Zquang-88/robocon-2026/hardwave/MP1584/d-sun-dc-dc-step-down-voltage-regulator-simple-version-1.snapshot.4/render/D-SUN_dcdc_step_down_SIMPLE1.png

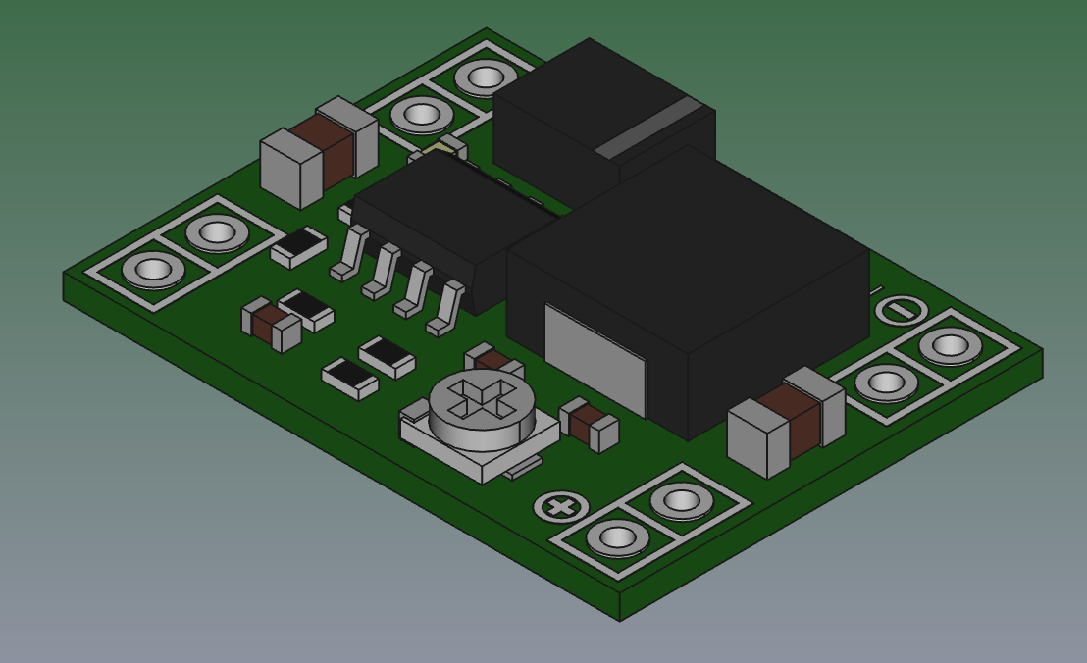
hardwave/MP1584/d-sun-dc-dc-step-down-voltage-regulator-simple-version-1.snapshot.4/render/D-SUN_dcdc_step_down_SIMPLE1.png
