Zquang-88/robocon-2026/.codex-analysis/latest-video-contact.jpg

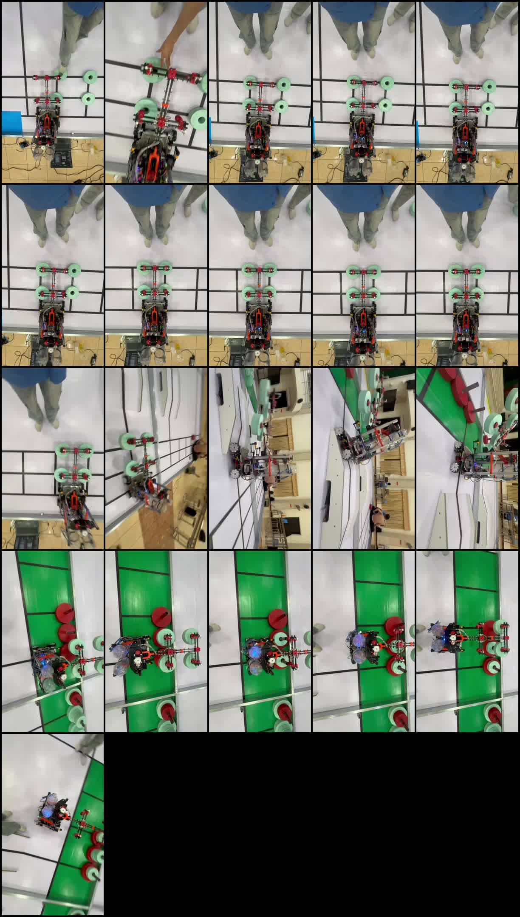
.codex-analysis/latest-video-contact.jpg
