Zquang-88/robocon-2026/analysis/bridge_flip_video/contact_2fps.jpg

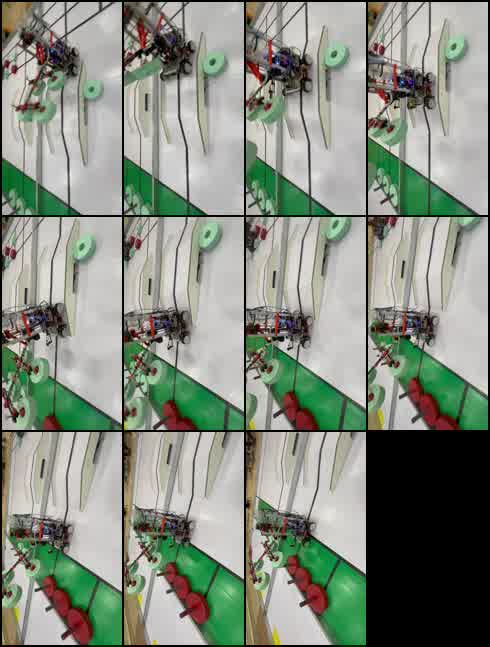
analysis/bridge_flip_video/contact_2fps.jpg
