Zquang-88/robocon-2026/analysis/bridge_flip_video/contact_5fps.jpg

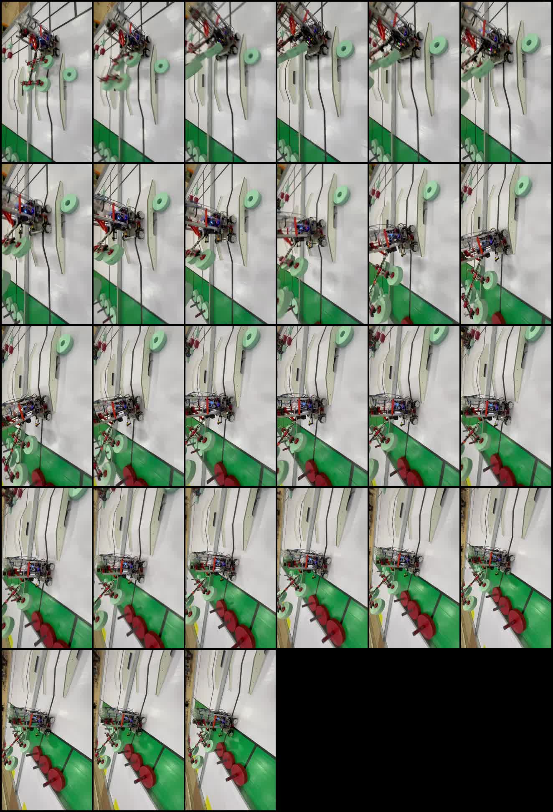
analysis/bridge_flip_video/contact_5fps.jpg
