Zquang-88/robocon-2026/analysis/bridge_flip_video/detail_2p8_5p3.jpg

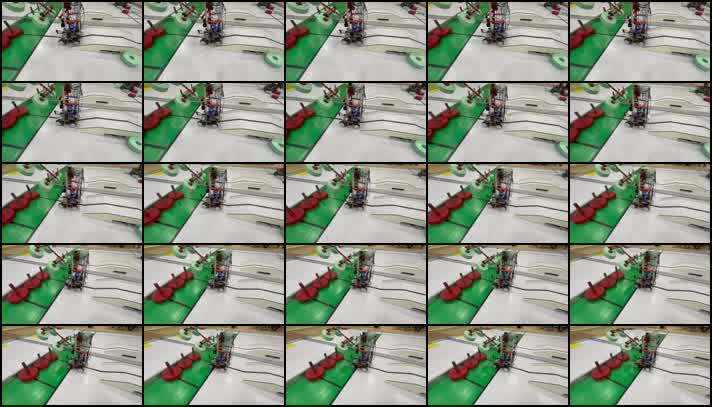
analysis/bridge_flip_video/detail_2p8_5p3.jpg
