Zquang-88/robocon-2026/analysis/bridge_flip_video/keyframes.jpg

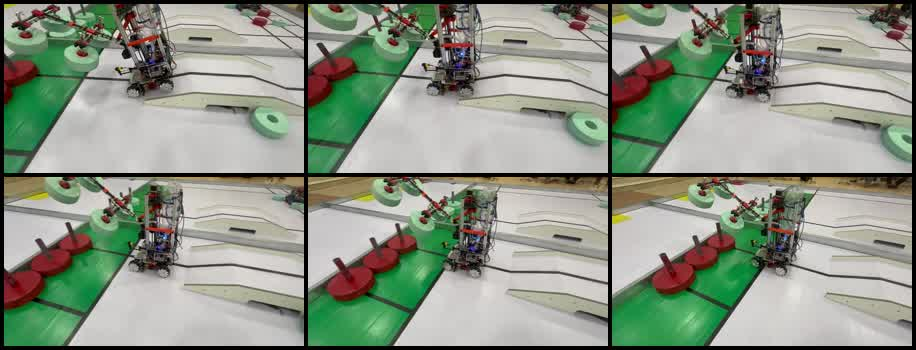
analysis/bridge_flip_video/keyframes.jpg
