Zquang-88/robocon-2026/analysis/bridge_flip_video/tip_sequence.jpg

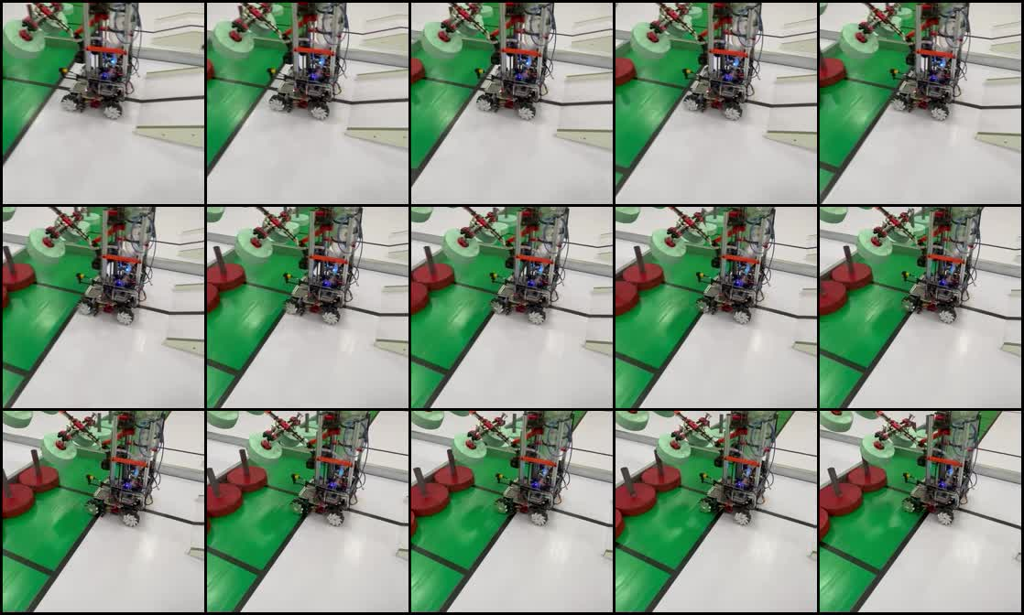
analysis/bridge_flip_video/tip_sequence.jpg
