Zquang-88/robocon-2026/analysis/bridge_run_sync/bridge_1fps.jpg

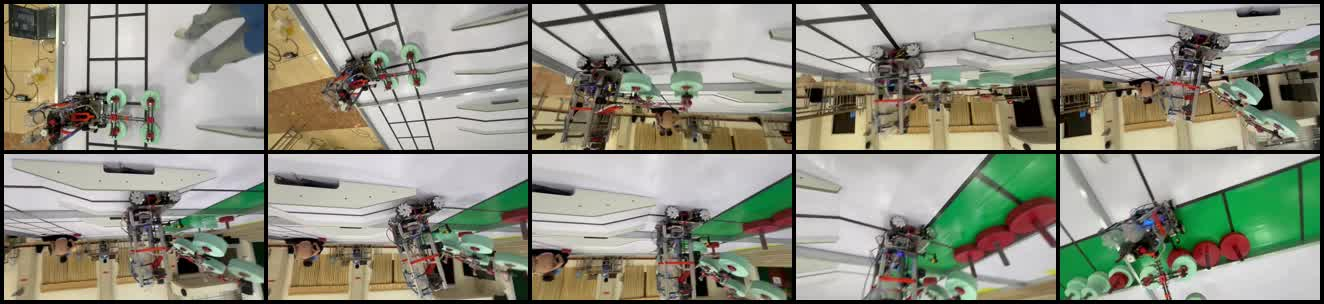
analysis/bridge_run_sync/bridge_1fps.jpg
