Zquang-88/robocon-2026/analysis/bridge_run_sync/descent_5fps.jpg

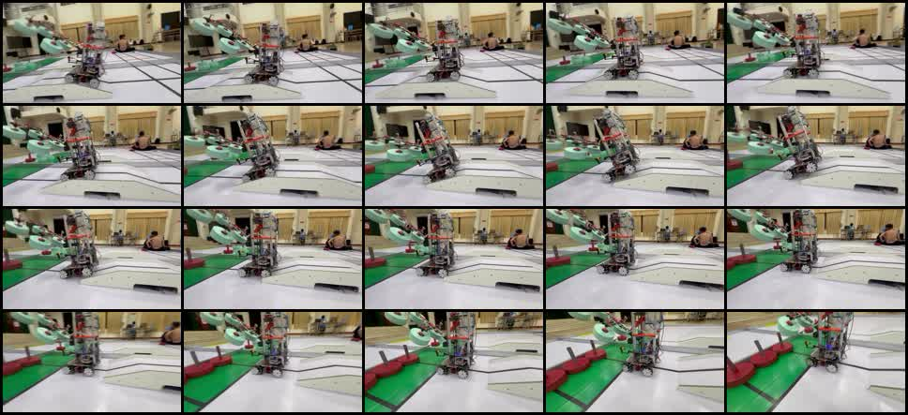
analysis/bridge_run_sync/descent_5fps.jpg
