Zquang-88/robocon-2026/analysis/bridge_run_sync/impact_10fps.jpg

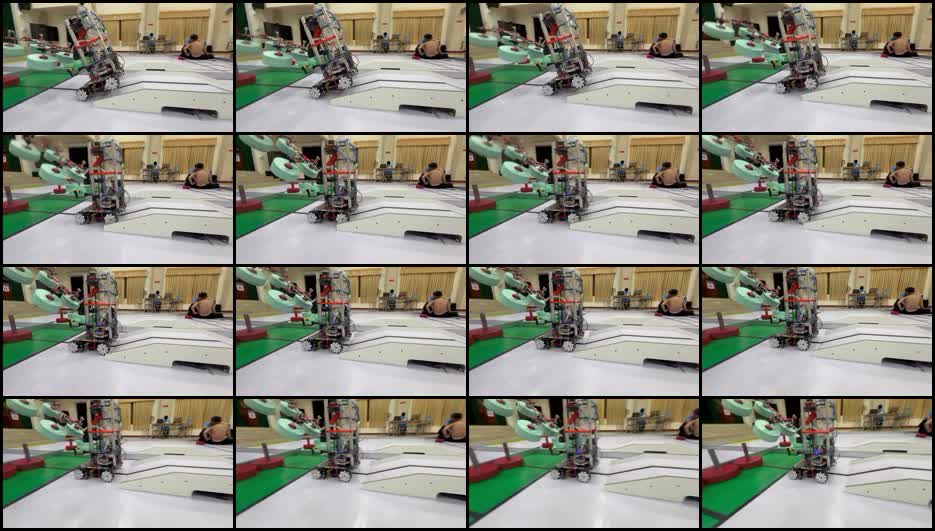
analysis/bridge_run_sync/impact_10fps.jpg
