Zquang-88/robocon-2026/analysis/bridge_run_sync/overview_2s.jpg

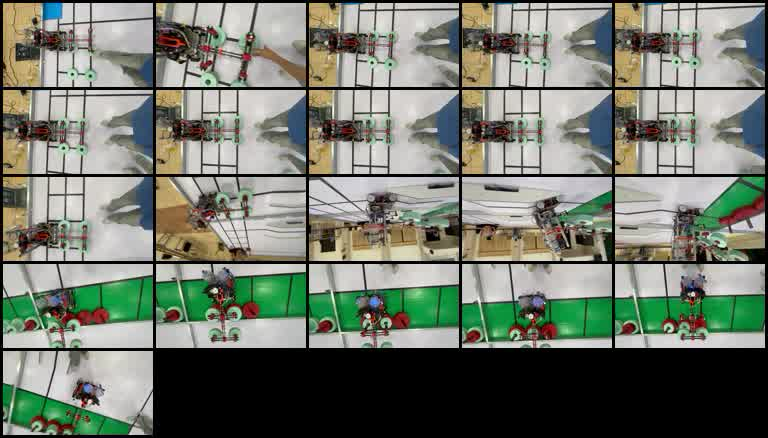
analysis/bridge_run_sync/overview_2s.jpg
