Zquang-88/robocon-2026/cad/buck-converter-lm2596-with-led-1.snapshot.1/LM2596_Led_render.png

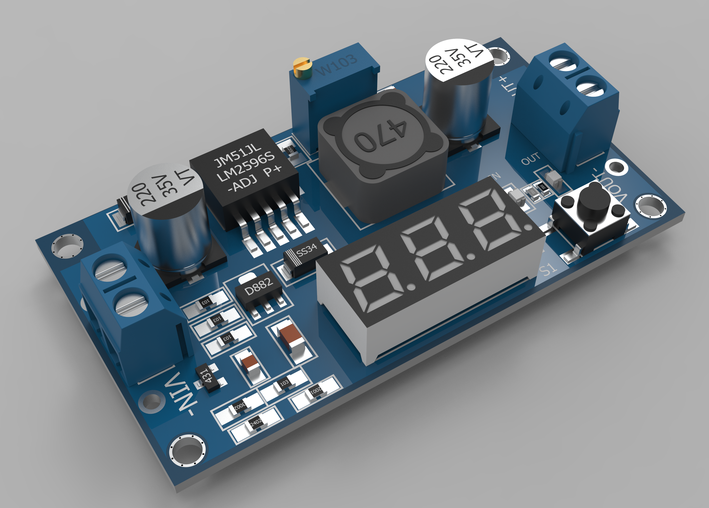
cad/buck-converter-lm2596-with-led-1.snapshot.1/LM2596_Led_render.png
