Zquang-88/robocon-2026/docs/.report_tmp/rendered_final/contact_sheets/pages-13-16.jpg

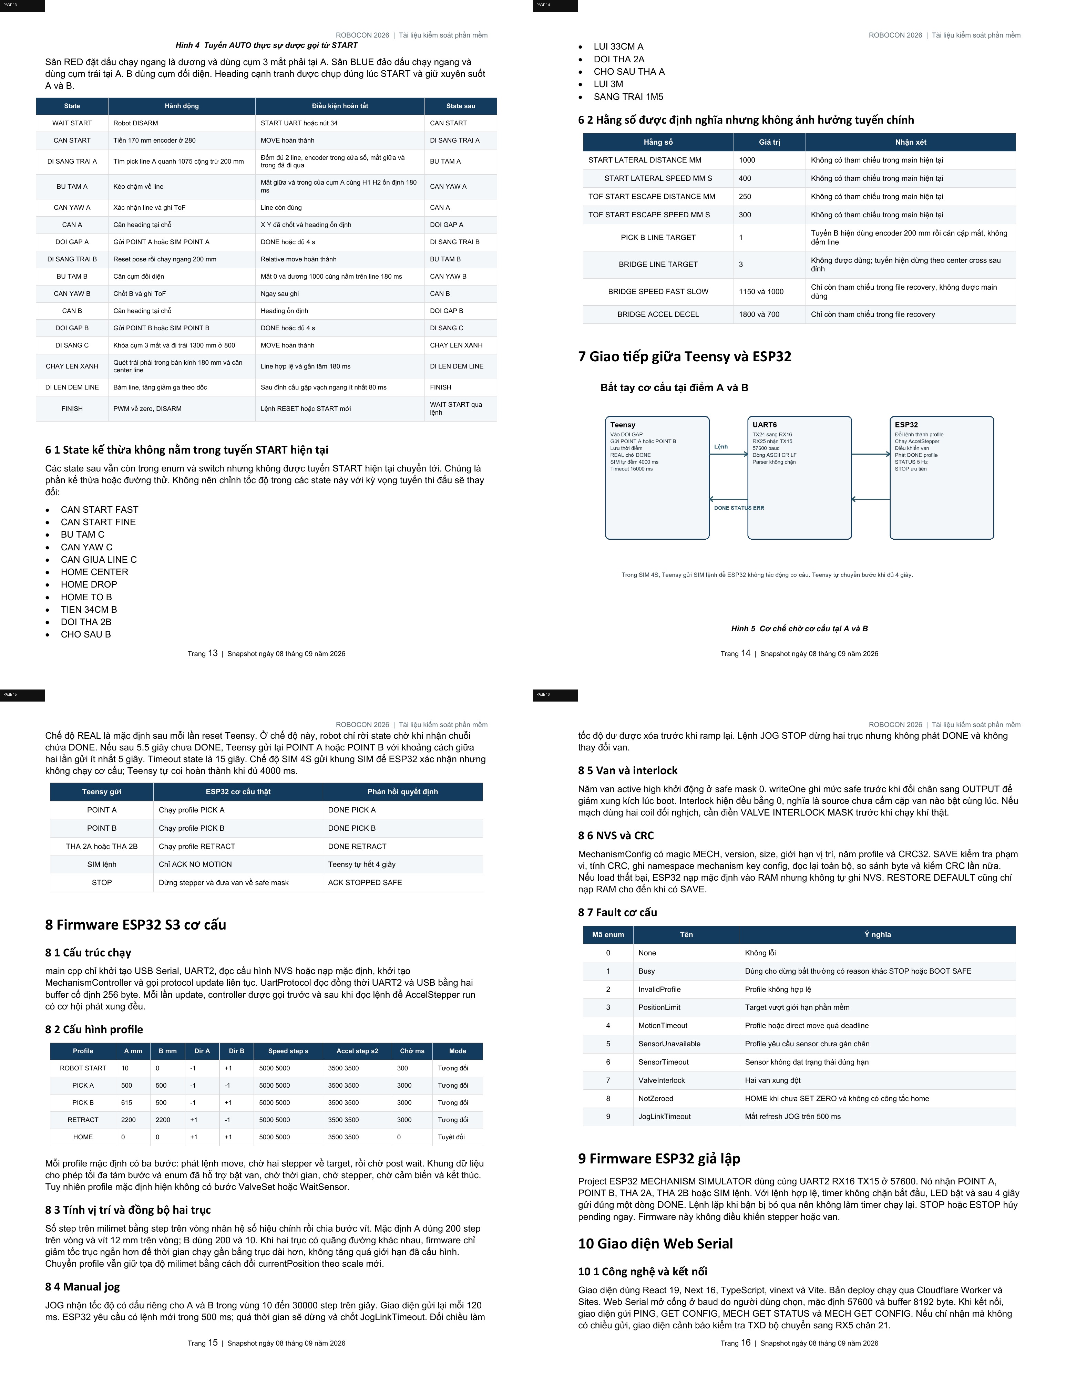
docs/.report_tmp/rendered_final/contact_sheets/pages-13-16.jpg
