Zquang-88/robocon-2026/docs/.report_tmp/rendered_final/page-1.png

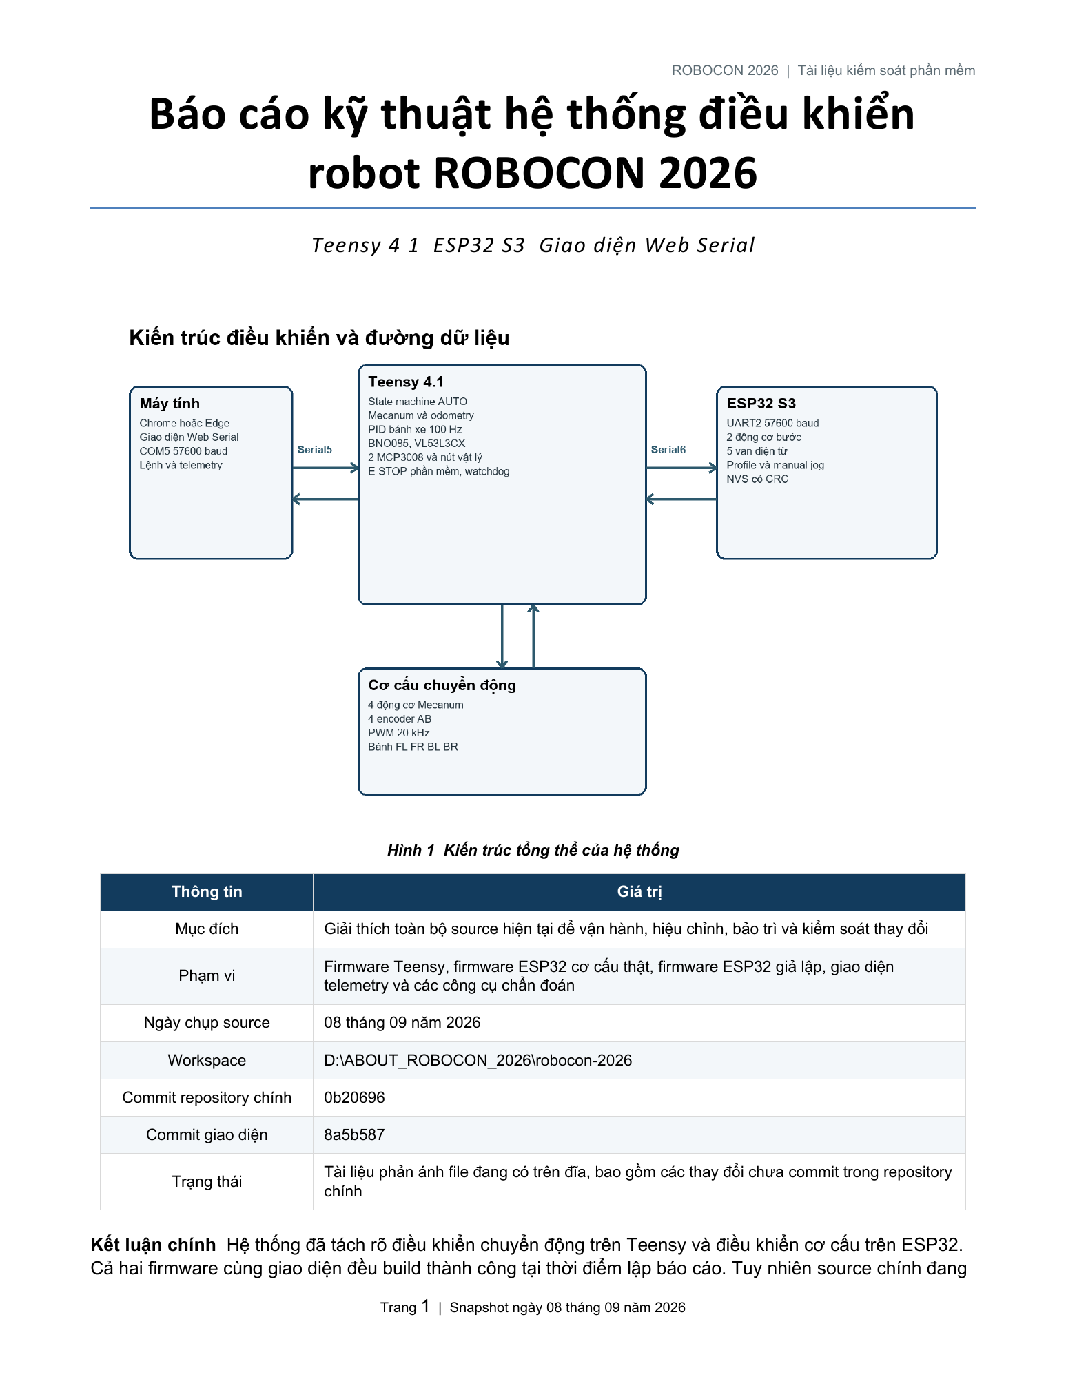
docs/.report_tmp/rendered_final/page-1.png
