Zquang-88/robocon-2026/docs/.report_tmp/rendered_final/page-10.png

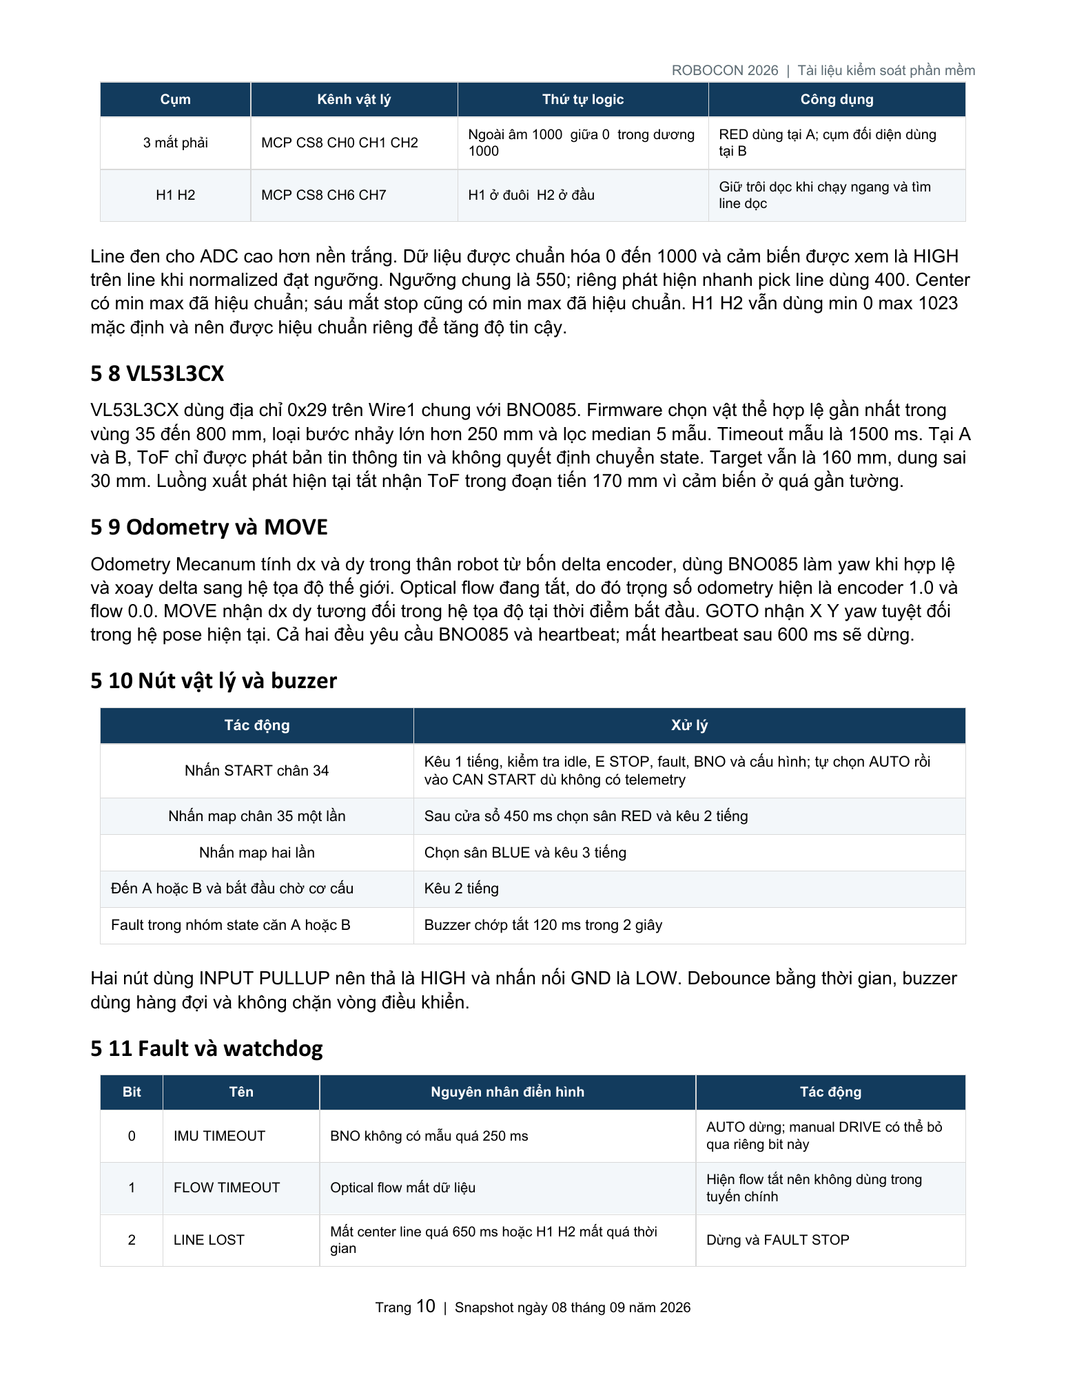
docs/.report_tmp/rendered_final/page-10.png
