Zquang-88/robocon-2026/docs/.report_tmp/rendered_final/page-24.png

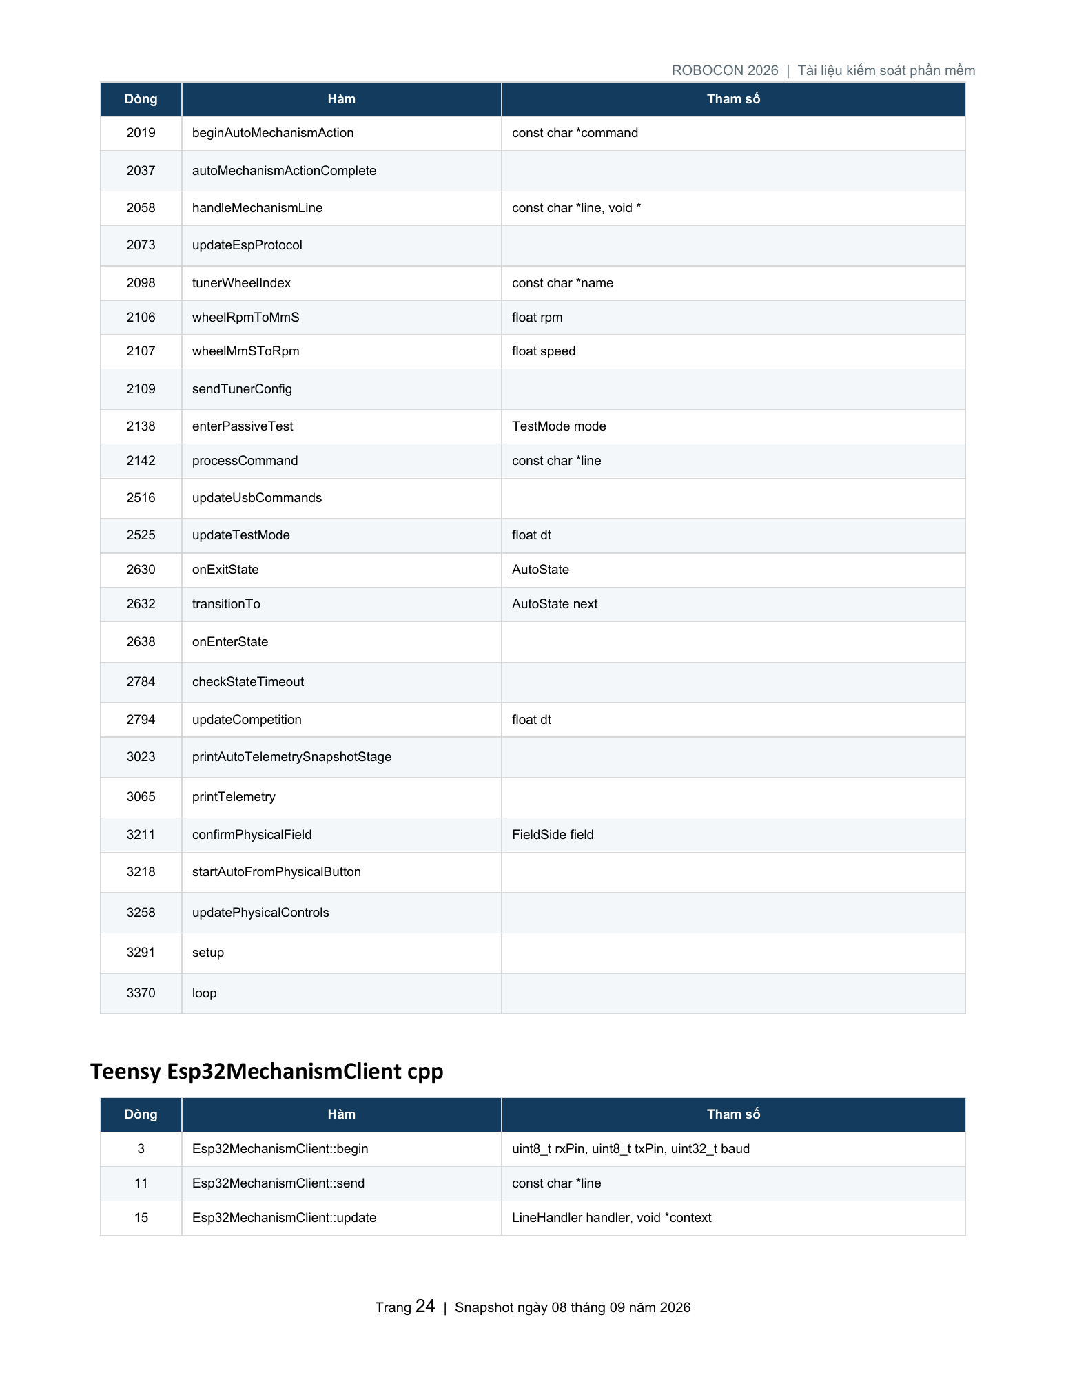
docs/.report_tmp/rendered_final/page-24.png
