Zquang-88/robocon-2026/docs/.report_tmp/rendered_final_v2/page-1.png

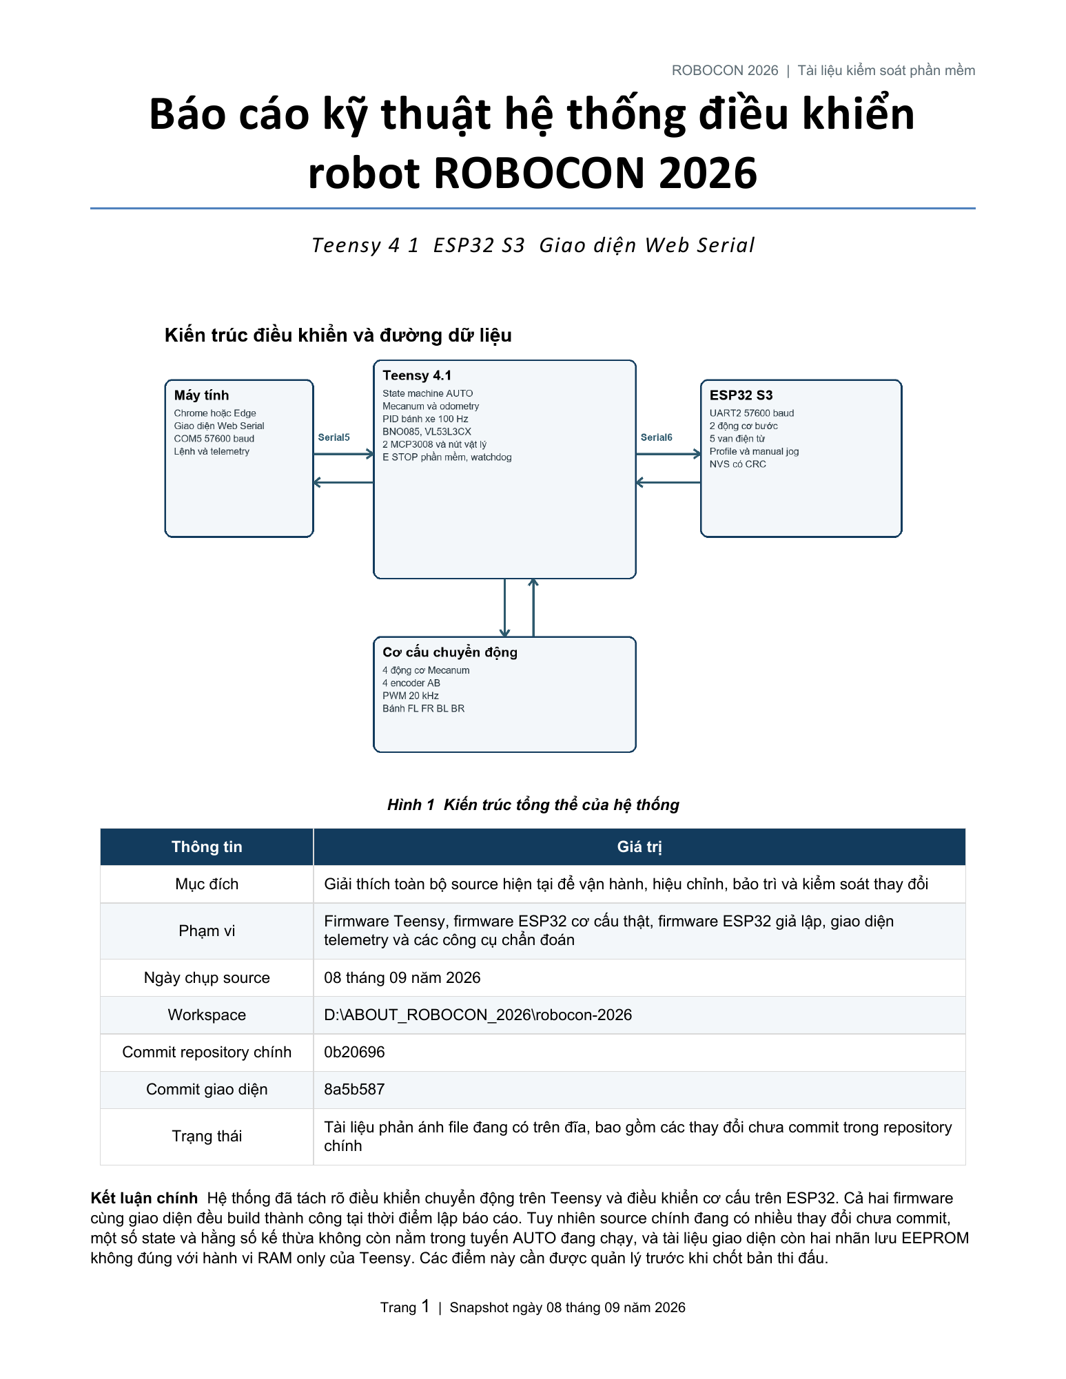
docs/.report_tmp/rendered_final_v2/page-1.png
