Zquang-88/robocon-2026/hardwave/ROBOCON_T9_LOGIC/pcb-spring-terminal-blocks-dg-142r-kf-142r-5-08-1.snapshot.16/5.JPG

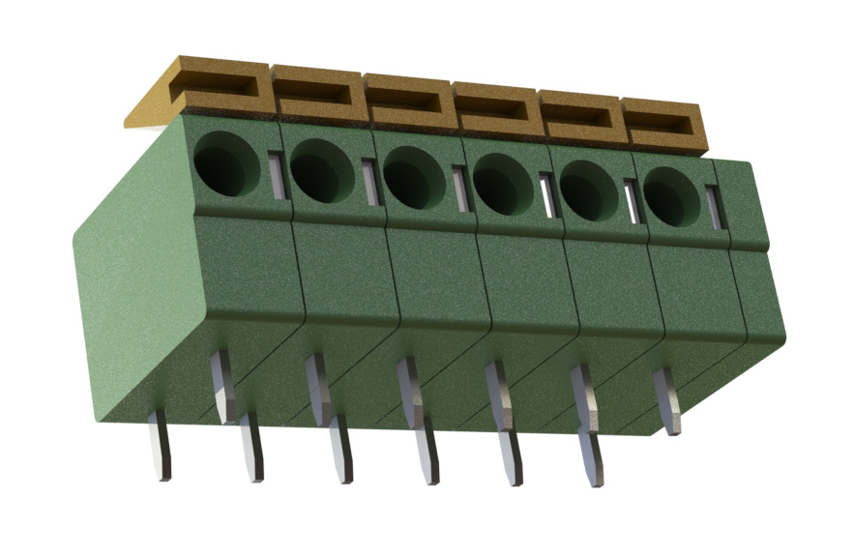
hardwave/ROBOCON_T9_LOGIC/pcb-spring-terminal-blocks-dg-142r-kf-142r-5-08-1.snapshot.16/5.JPG
