Zquang-88/robocon-2026/cad/demo đế v2/ĐẾ TRƯỚC.step

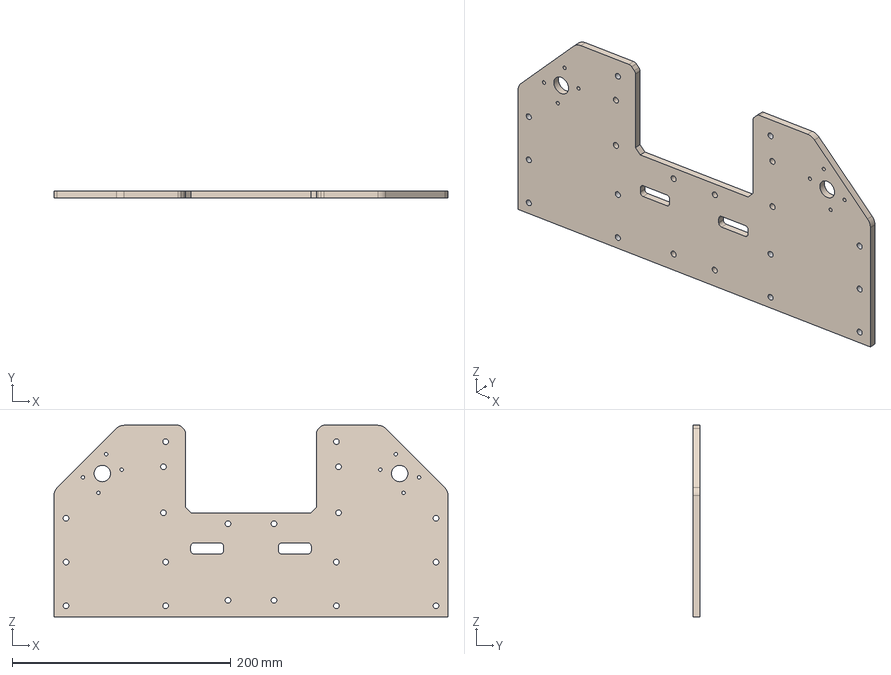
[picture p88: CAD file, 2026-07-30]
cad/demo đế v2/ĐẾ TRƯỚC.step
360.0 x 6.00 x 175.0 mm
