Zquang-88/robocon-2026/cad/KHOA_CHUONG_HEO/11.step

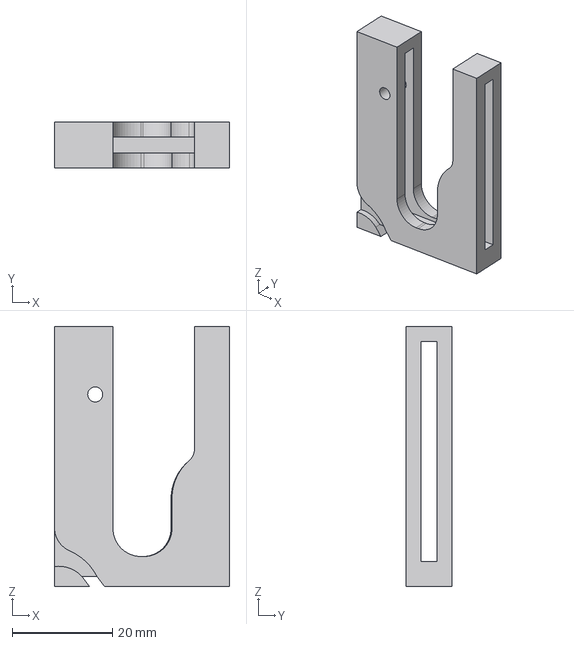
[picture p89: CAD file, 2026-08-18]
cad/KHOA_CHUONG_HEO/11.step
35.0 x 9.10 x 52.0 mm
