Zquang-88/robocon-2026/cad/TẤM ĐẾ PHAY.step

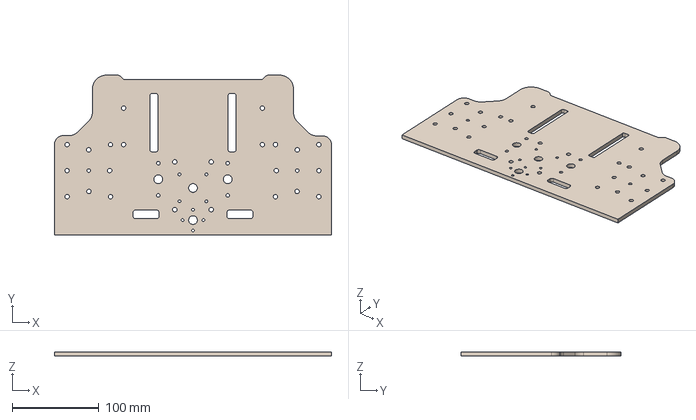
[picture p90: CAD file, 2026-08-21]
cad/TẤM ĐẾ PHAY.step
319.2 x 184.0 x 5.00 mm
