Zquang-88/robocon-2026/hardwave/MP1584/d-sun-dc-dc-step-down-voltage-regulator-simple-version-1.snapshot.4/components/C0603_simple.step

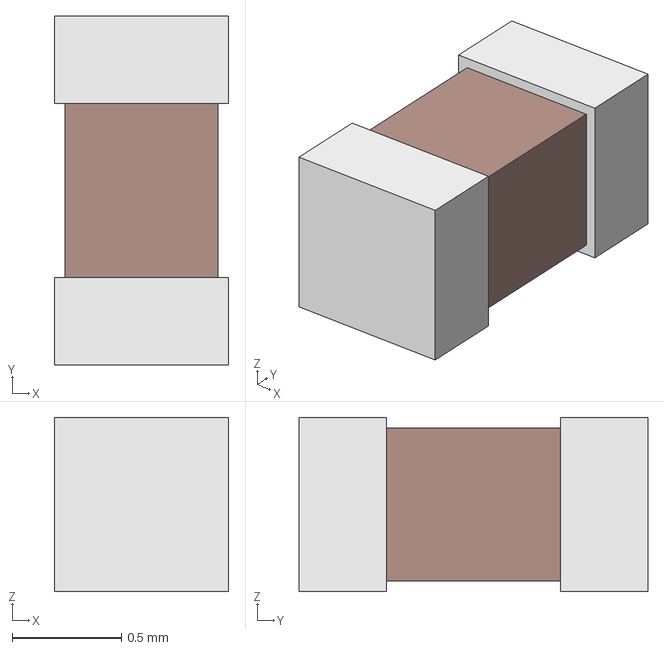
[picture p91: CAD file, 2026-07-30]
hardwave/MP1584/d-sun-dc-dc-step-down-voltage-regulator-simple-version-1.snapshot.4/components/C0603_simple.step
0.8 x 1.60 x 0.8 mm
