Zquang-88/robocon-2026/hardwave/MP1584/d-sun-dc-dc-step-down-voltage-regulator-simple-version-1.snapshot.4/D-SUN_dcdc_step_down_Simple_NoSilk_.step

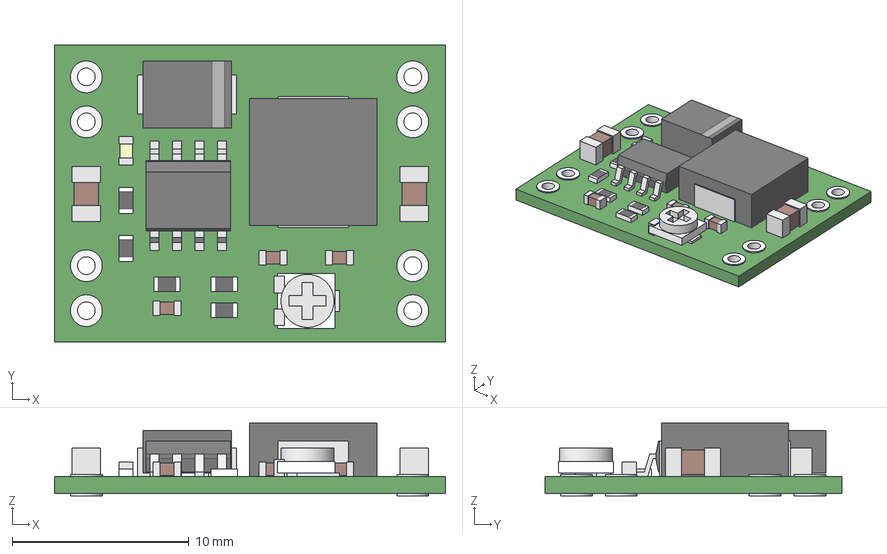
[picture p92: CAD file, 2026-07-30]
hardwave/MP1584/d-sun-dc-dc-step-down-voltage-regulator-simple-version-1.snapshot.4/D-SUN_dcdc_step_down_Simple_NoSilk_.step
22.1 x 16.8 x 4.10 mm
main001
pins
comp-top
