Zquang-88/robocon-2026/cad/KHOA_CHUONG_HEO/Part3.SLDPRT

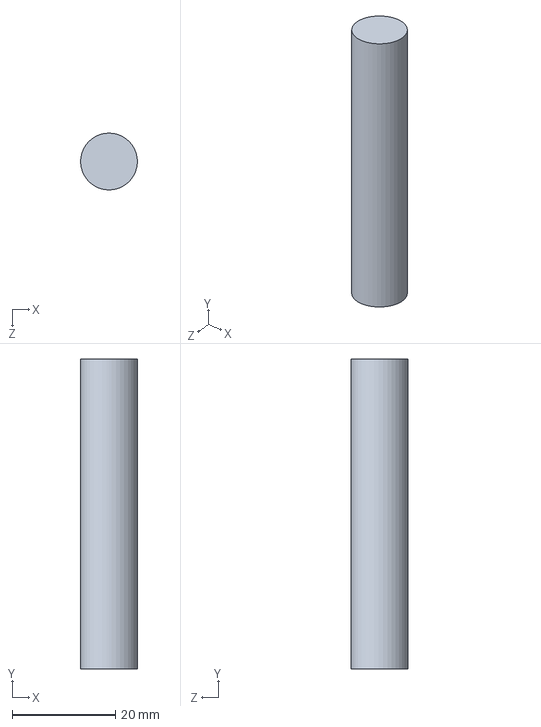
[picture p93: CAD file, 2026-08-18]
cad/KHOA_CHUONG_HEO/Part3.SLDPRT
11.0 x 60.0 x 11.0 mm
