Zquang-88/robocon-2026/hardwave/MP1584/d-sun-dc-dc-step-down-voltage-regulator-simple-version-1.snapshot.4/components/SO-8_narrow_simple.step

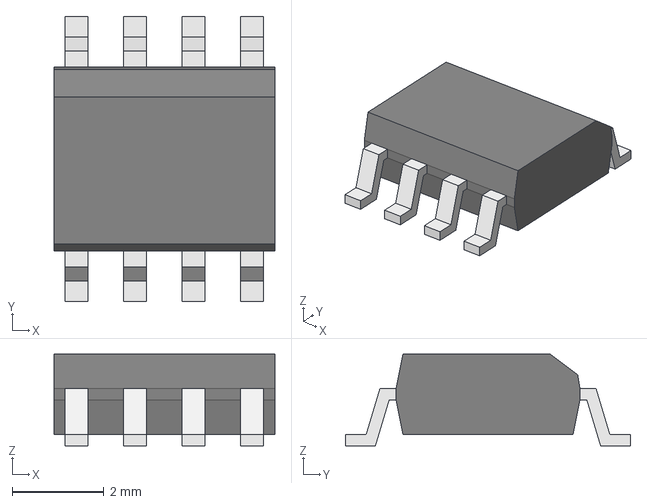
[picture p94: CAD file, 2026-07-30]
hardwave/MP1584/d-sun-dc-dc-step-down-voltage-regulator-simple-version-1.snapshot.4/components/SO-8_narrow_simple.step
4.80 x 6.20 x 2.00 mm
