Zquang-88/robocon-2026/cad/demo đế v2/CẢ KHUNG ĐẾ.step

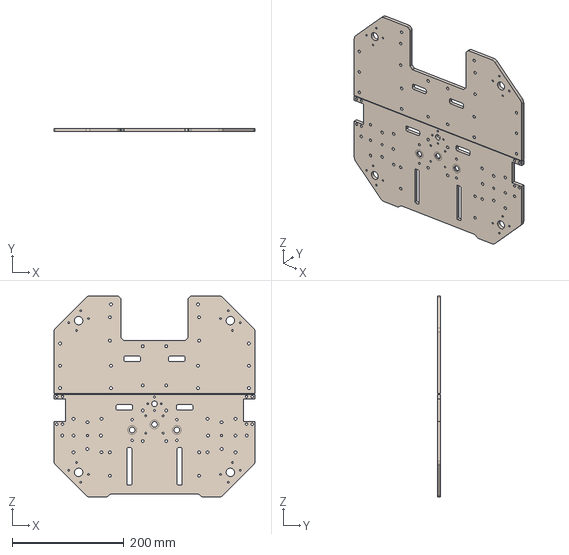
[picture p95: CAD file, 2026-07-30]
cad/demo đế v2/CẢ KHUNG ĐẾ.step
360.0 x 6.00 x 360.0 mm
