Zquang-88/robocon-2026/hardwave/MP1584/d-sun-dc-dc-step-down-voltage-regulator-simple-version-1.snapshot.4/components/DO-214AA_simple.step

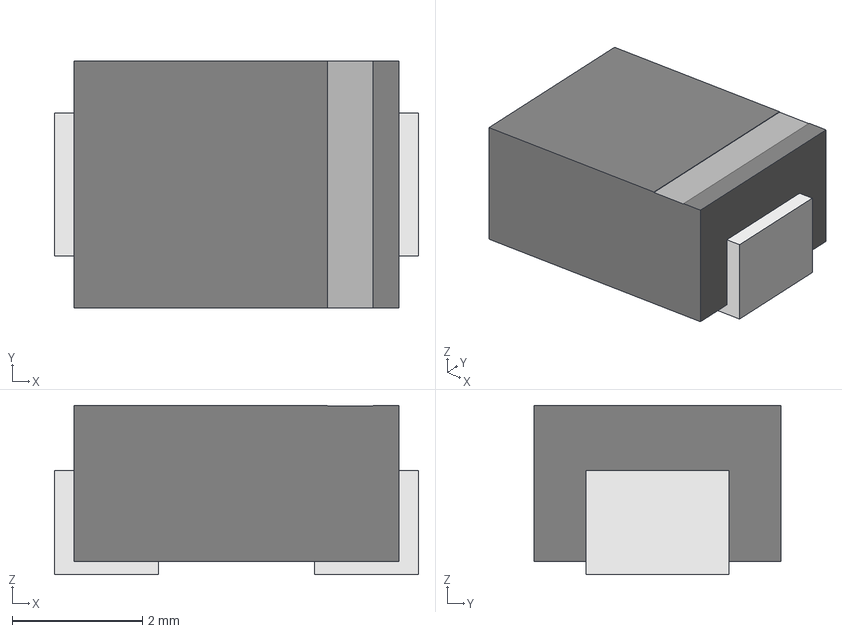
[picture p96: CAD file, 2026-07-30]
hardwave/MP1584/d-sun-dc-dc-step-down-voltage-regulator-simple-version-1.snapshot.4/components/DO-214AA_simple.step
5.60 x 3.80 x 2.60 mm
