Zquang-88/robocon-2026/cad/demo đế v2/đế sau .step

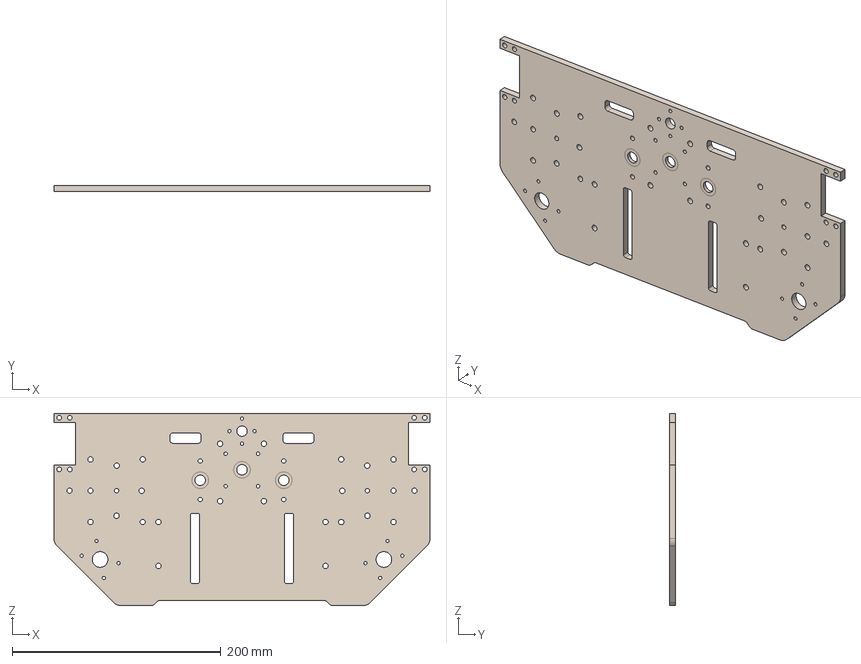
[picture p97: CAD file, 2026-07-30]
cad/demo đế v2/đế sau .step
360.0 x 6.00 x 184.0 mm
