Zquang-88/robocon-2026/hardwave/MP1584/d-sun-dc-dc-step-down-voltage-regulator-simple-version-1.snapshot.4/components/R_EVM-3E_simple.FCStd

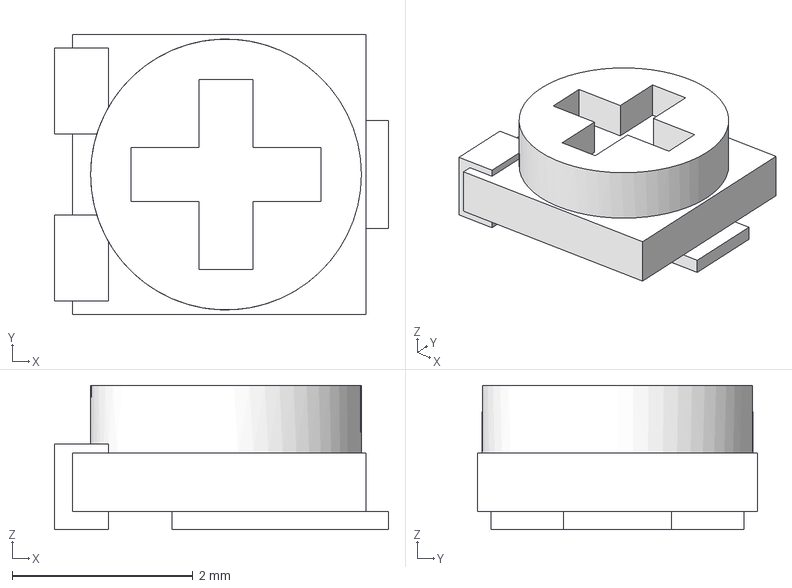
[picture p98: CAD file, 2026-07-30]
hardwave/MP1584/d-sun-dc-dc-step-down-voltage-regulator-simple-version-1.snapshot.4/components/R_EVM-3E_simple.FCStd
3.70 x 3.10 x 1.60 mm
