Zquang-88/robocon-2026/hardwave/ROBOCON_T9_V1/esp32-s3-wroom-1-1.snapshot.2/RC0402.SLDPRT

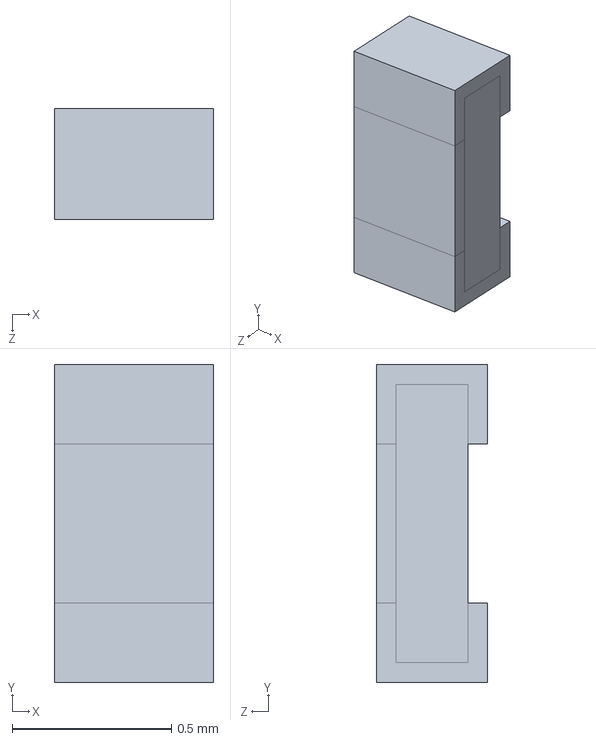
[picture p99: CAD file, 2026-07-18]
hardwave/ROBOCON_T9_V1/esp32-s3-wroom-1-1.snapshot.2/RC0402.SLDPRT
0.5 x 1.00 x 0.35 mm
