Zquang-88/robocon-2026/hardwave/MP1584/d-sun-dc-dc-step-down-voltage-regulator-simple-version-1.snapshot.4/components/C0805_H1.6_simple.step

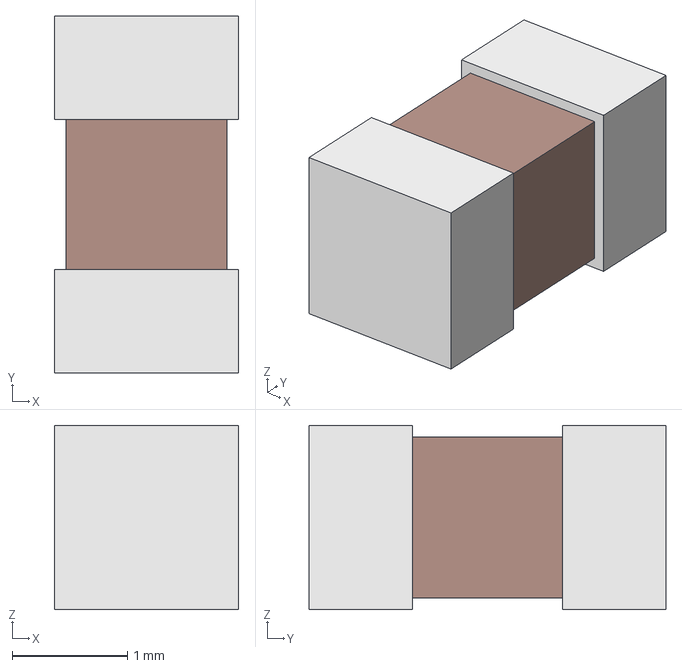
[picture p100: CAD file, 2026-07-30]
hardwave/MP1584/d-sun-dc-dc-step-down-voltage-regulator-simple-version-1.snapshot.4/components/C0805_H1.6_simple.step
1.60 x 3.10 x 1.60 mm
