Zquang-88/robocon-2026/hardwave/ROBOCON_T9_V1/esp32-s3-wroom-1-1.snapshot.2/ESP32-S3-WROOM-1.STEP

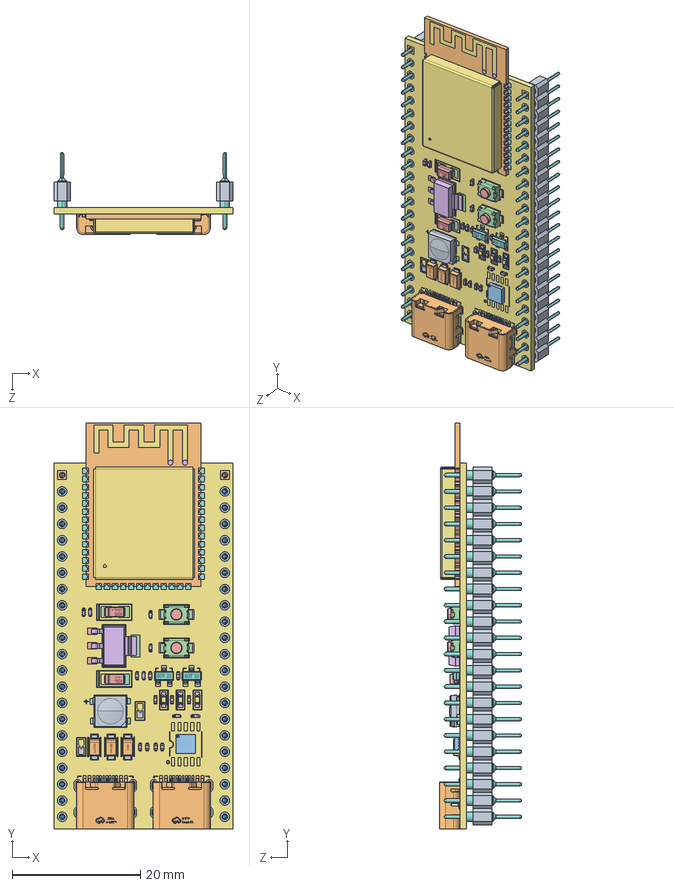
[picture p101: CAD file, 2026-07-18]
hardwave/ROBOCON_T9_V1/esp32-s3-wroom-1-1.snapshot.2/ESP32-S3-WROOM-1.STEP
27.9 x 63.4 x 12.9 mm
ESP32-S3-WROOM-1
Штыревой разъем 22 конт шаг 2.54мм x 2
USB-C_SMD-TYPE-C-31-M-12~USB-C_SMD-TYPE-C-31-M-12~QTmk.step.STEP x 2
2025-08-30-17-43-03-310.step.STEP x 2
WS2812B
SOT-223
SOT23-3 x 2
SOD-123F x 3
QFN-16 (3x3) Part1.stp
QFN-16 (3x3) Part2.stp x 16
ctantal_case-a_l3-2_w1-6_h1-6 x 2
Body.step x 3
Cover.step x 3
Cover_Mini.step x 3
Insides.step x 3
RC0402 x 10
0402_CA_CB_CC_CD x 7
