Zquang-88/robocon-2026/hardwave/ROBOCON_T9_V1/esp32-s3-wroom-1-1.snapshot.2/SOT-223.SLDPRT

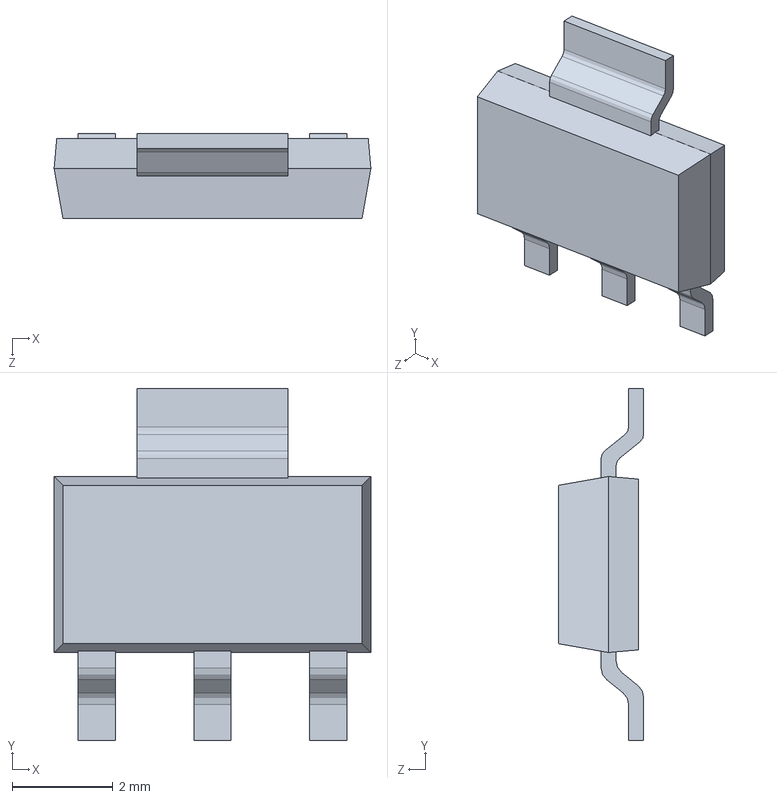
[picture p103: CAD file, 2026-07-18]
hardwave/ROBOCON_T9_V1/esp32-s3-wroom-1-1.snapshot.2/SOT-223.SLDPRT
6.30 x 7.00 x 1.70 mm
