Zquang-88/robocon-2026/hardwave/ROBOCON_T9_V1/esp32-s3-wroom-1-1.snapshot.2/Штыревой разъем 22 конт шаг 2.54мм.SLDPRT

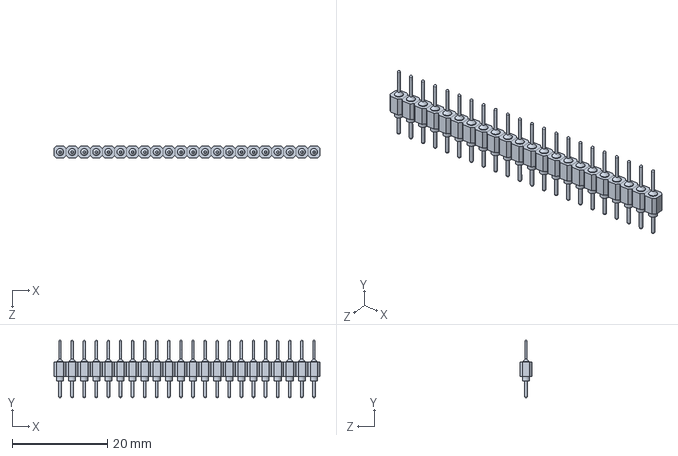
[picture p104: CAD file, 2026-07-18]
hardwave/ROBOCON_T9_V1/esp32-s3-wroom-1-1.snapshot.2/Штыревой разъем 22 конт шаг 2.54мм.SLDPRT
55.9 x 12.1 x 2.54 mm
