Zquang-88/robocon-2026/hardwave/ROBOCON_T9_V1/esp32-s3-wroom-1-1.snapshot.2/0402_CA_CB_CC_CD.SLDPRT

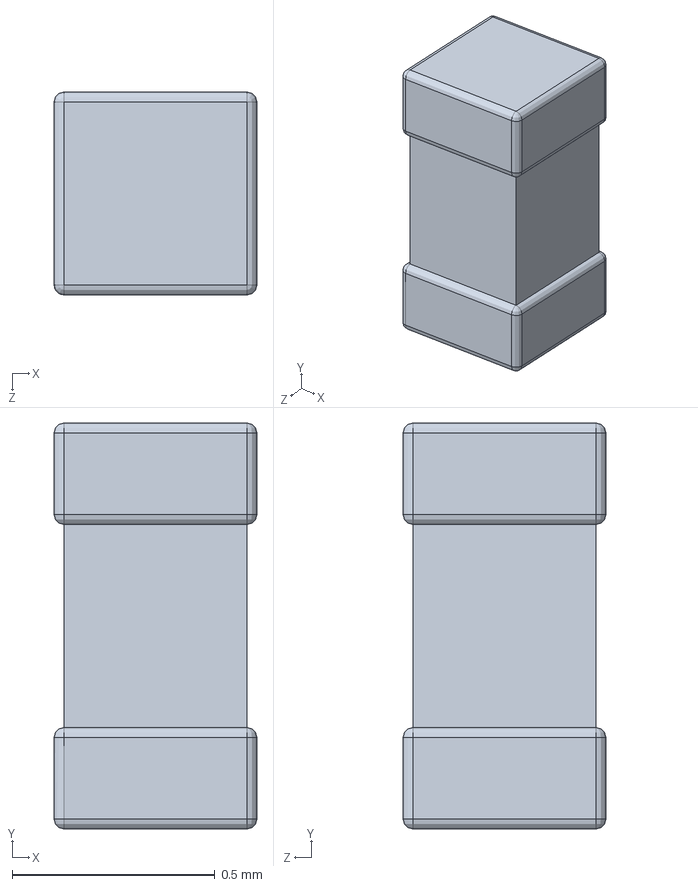
[picture p105: CAD file, 2026-07-18]
hardwave/ROBOCON_T9_V1/esp32-s3-wroom-1-1.snapshot.2/0402_CA_CB_CC_CD.SLDPRT
0.5 x 1.00 x 0.5 mm
