Zquang-88/robocon-2026/hardwave/ROBOCON_T9_V1/esp32-s3-wroom-1-1.snapshot.2/SOT23-3.SLDPRT

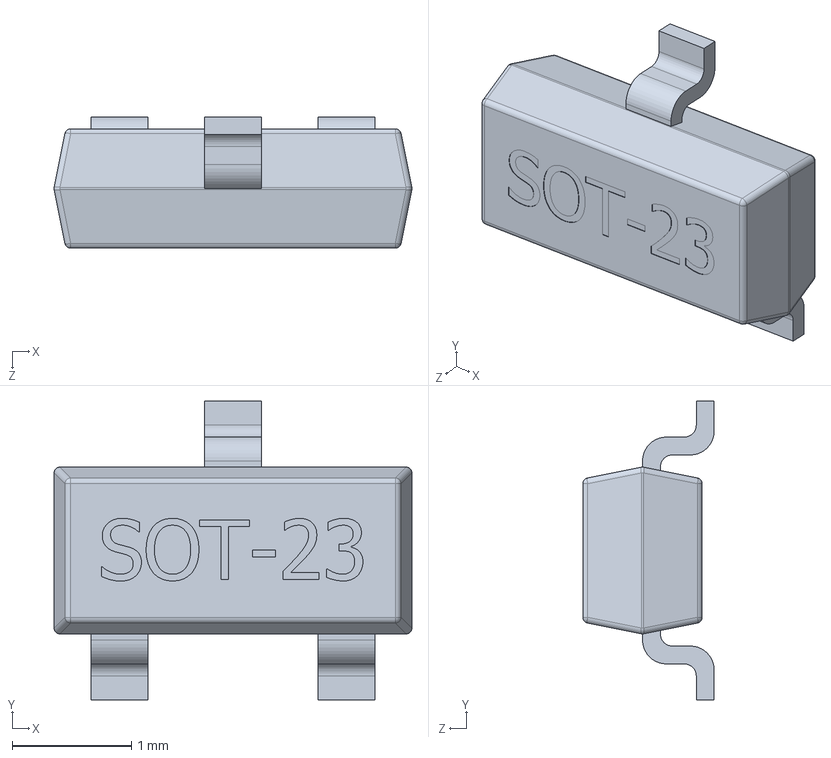
[picture p106: CAD file, 2026-07-18]
hardwave/ROBOCON_T9_V1/esp32-s3-wroom-1-1.snapshot.2/SOT23-3.SLDPRT
3.00 x 2.50 x 1.10 mm
