Zquang-88/robocon-2026/hardwave/ROBOCON_T9_V1/esp32-s3-wroom-1-1.snapshot.2/SOD-123F.SLDPRT

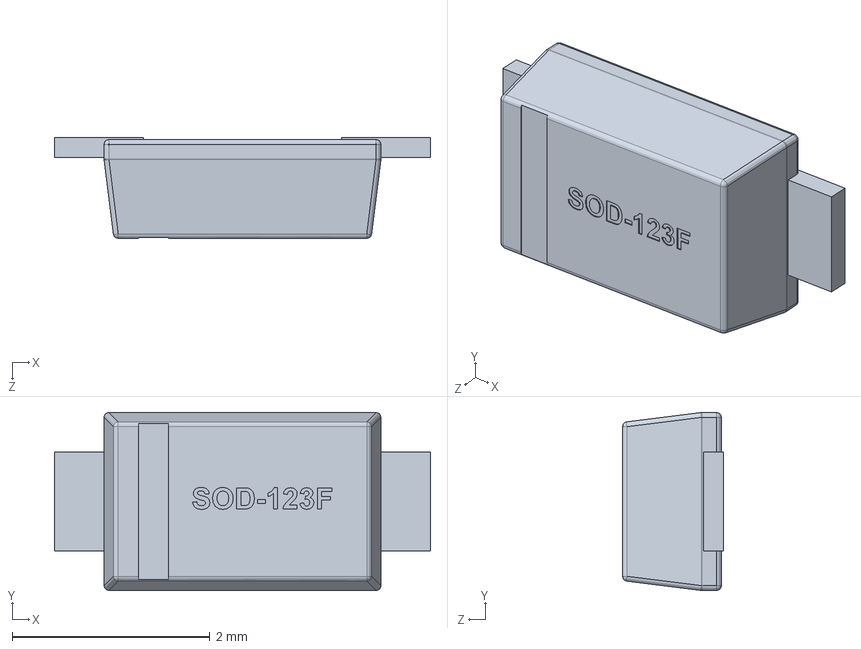
[picture p107: CAD file, 2026-07-18]
hardwave/ROBOCON_T9_V1/esp32-s3-wroom-1-1.snapshot.2/SOD-123F.SLDPRT
3.80 x 1.80 x 1.02 mm
