Zquang-88/robocon-2026/hardwave/ROBOCON_T9_V1/esp32-s3-wroom-1-1.snapshot.2/WS2812B.SLDPRT

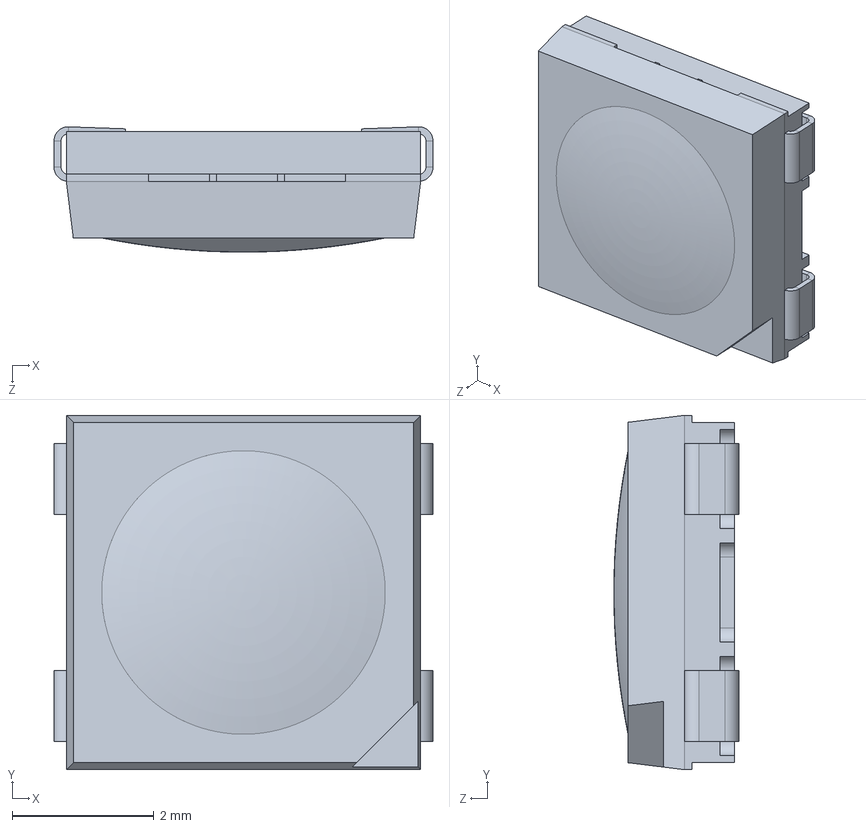
[picture p108: CAD file, 2026-07-18]
hardwave/ROBOCON_T9_V1/esp32-s3-wroom-1-1.snapshot.2/WS2812B.SLDPRT
5.35 x 5.00 x 1.77 mm
