Zquang-88/robocon-2026/hardwave/ROBOCON_T9_V1/esp32-s3-wroom-1-1.snapshot.2/ctantal_case-a_l3-2_w1-6_h1-6.SLDPRT

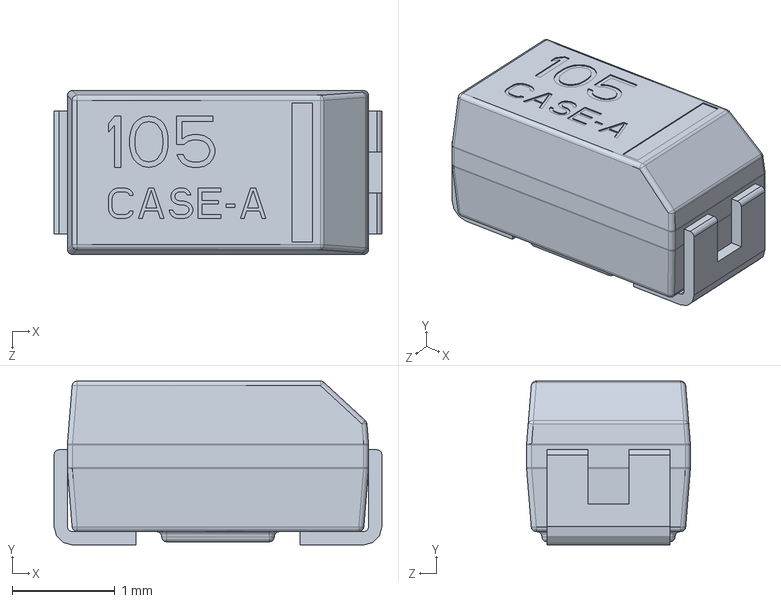
[picture p109: CAD file, 2026-07-18]
hardwave/ROBOCON_T9_V1/esp32-s3-wroom-1-1.snapshot.2/ctantal_case-a_l3-2_w1-6_h1-6.SLDPRT
3.20 x 1.60 x 1.60 mm
