Zquang-88/robocon-2026/analysis/manual_motion_videos/1789266678602_53441593253659687_6409918754985055598_trajectory.png

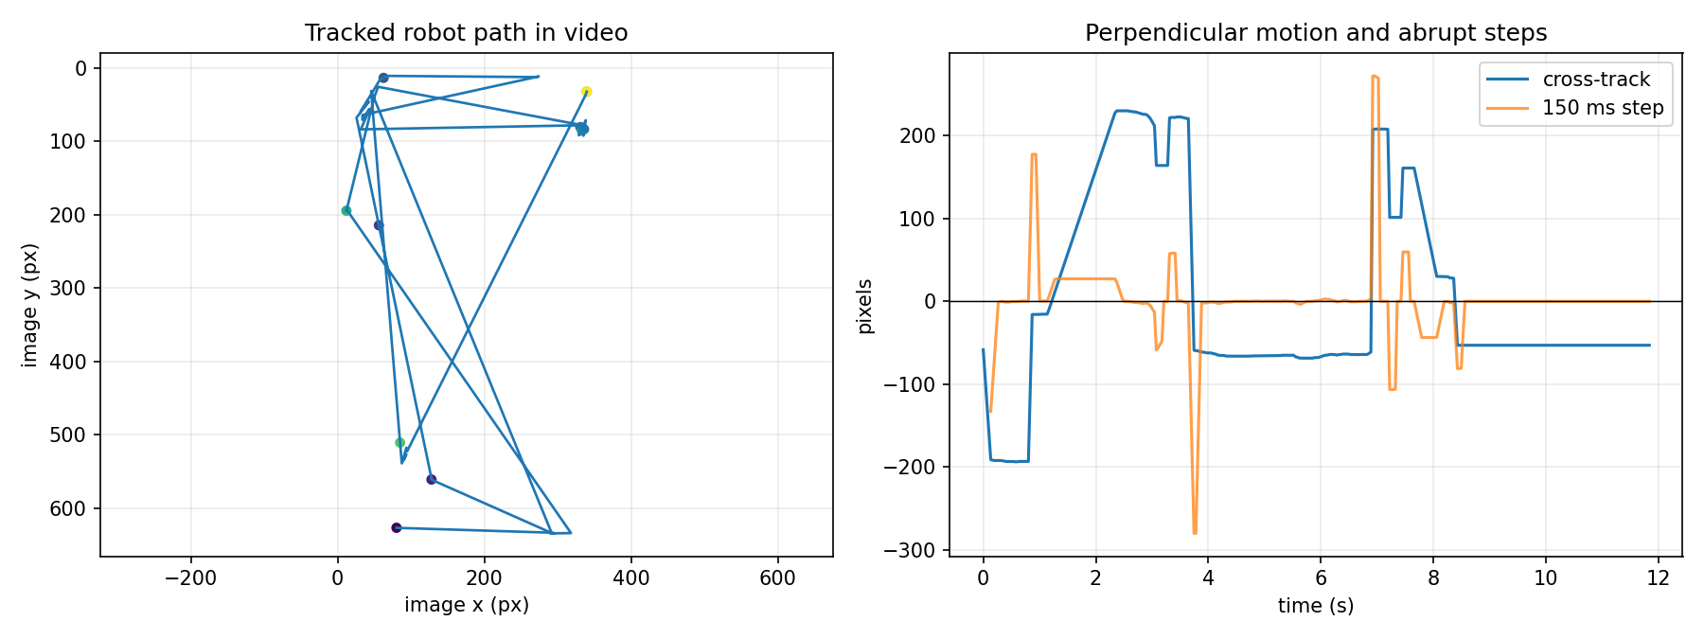
analysis/manual_motion_videos/1789266678602_53441593253659687_6409918754985055598_trajectory.png
