Zquang-88/robocon-2026/analysis/manual_motion_videos/video1_burst.jpg

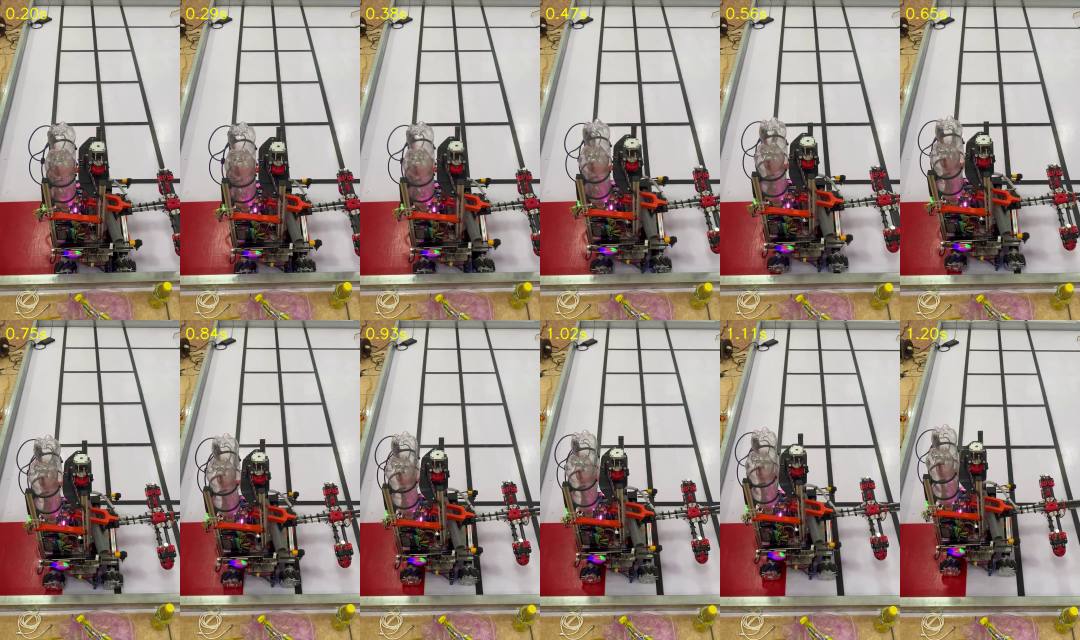
analysis/manual_motion_videos/video1_burst.jpg
