Zquang-88/robocon-2026/firmwave/ROBOCON_KOSEN_F0/wheel_tune_loaded_ff_blneg_final.csv

host_s | segment | direction | command_mm_s | record | wheel | target_rpm | actual_rpm | pwm | encoder | yaw_deg | yaw_target_deg | yaw_error_deg
1.5 | -1 | IDLE | 0 | WHEEL | FR | 0.00 | 0.00 | 0 | -716
1.5 | -1 | IDLE | 0 | WHEEL | BL | 0.00 | 0.00 | 0 | -337
1.5 | -1 | IDLE | 0 | WHEEL | BR | 0.00 | 0.00 | 0 | 525
1.5160000000032596 | -1 | IDLE | 0 | HDG |  |  |  |  |  | 6.82 | 6.81 | -0.01
1.5160000000032596 | -1 | IDLE | 0 | WHEEL | FL | 0.00 | 0.00 | 0 | 440
1.5160000000032596 | -1 | IDLE | 0 | WHEEL | FR | 0.00 | 0.00 | 0 | -716
1.5160000000032596 | -1 | IDLE | 0 | WHEEL | BL | 0.00 | 0.00 | 0 | -337
1.5160000000032596 | -1 | IDLE | 0 | WHEEL | BR | 0.00 | 0.00 | 0 | 525
1.5160000000032596 | -1 | IDLE | 0 | HDG |  |  |  |  |  | 6.82 | 6.81 | -0.01
1.5320000000065193 | -1 | IDLE | 0 | WHEEL | FL | 0.00 | 0.00 | 0 | 440
1.5320000000065193 | -1 | IDLE | 0 | WHEEL | FR | 0.00 | 0.00 | 0 | -716
1.5320000000065193 | -1 | IDLE | 0 | WHEEL | BL | 0.00 | 0.00 | 0 | -337
1.5320000000065193 | -1 | IDLE | 0 | WHEEL | BR | 0.00 | 0.00 | 0 | 525
1.5320000000065193 | -1 | IDLE | 0 | HDG |  |  |  |  |  | 6.82 | 6.81 | -0.01
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
