Zquang-88/robocon-2026/firmwave/ROBOCON_KOSEN_F0/wheel_tune_loaded_ff_blneg_trim.csv

host_s | segment | direction | command_mm_s | record | wheel | target_rpm | actual_rpm | pwm | encoder | yaw_deg | yaw_target_deg | yaw_error_deg
1.5150000000139698 | -1 | IDLE | 0 | WHEEL | FR | 0.00 | 0.00 | 0 | -683
1.5150000000139698 | -1 | IDLE | 0 | WHEEL | BL | 0.00 | 0.00 | 0 | -475
1.5150000000139698 | -1 | IDLE | 0 | WHEEL | BR | 0.00 | 0.00 | 0 | 547
1.5150000000139698 | -1 | IDLE | 0 | HDG |  |  |  |  |  | 3.13 | 3.28 | 0.15
1.5310000000172295 | -1 | IDLE | 0 | WHEEL | FL | 0.00 | 0.00 | 0 | 506
1.5310000000172295 | -1 | IDLE | 0 | WHEEL | FR | 0.00 | 0.00 | 0 | -683
1.5310000000172295 | -1 | IDLE | 0 | WHEEL | BL | 0.00 | 0.00 | 0 | -475
1.5310000000172295 | -1 | IDLE | 0 | WHEEL | BR | 0.00 | 0.00 | 0 | 547
1.5310000000172295 | -1 | IDLE | 0 | HDG |  |  |  |  |  | 3.13 | 3.28 | 0.15
1.5310000000172295 | -1 | IDLE | 0 | WHEEL | FL | 0.00 | 0.00 | 0 | 506
1.5310000000172295 | -1 | IDLE | 0 | WHEEL | FR | 0.00 | 0.00 | 0 | -683
1.5310000000172295 | -1 | IDLE | 0 | WHEEL | BL | 0.00 | 0.00 | 0 | -475
1.5310000000172295 | -1 | IDLE | 0 | WHEEL | BR | 0.00 | 0.00 | 0 | 547
1.5310000000172295 | -1 | IDLE | 0 | HDG |  |  |  |  |  | 3.13 | 3.28 | 0.15
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
