Zquang-88/robocon-2026/firmwave/ROBOCON_KOSEN_F0/wheel_tune_loaded_ff_low.csv

host_s | segment | direction | command_mm_s | record | wheel | target_rpm | actual_rpm | pwm | encoder | yaw_deg | yaw_target_deg | yaw_error_deg
1.5 | -1 | IDLE | 0 | WHEEL | FR | 0.00 | 0.00 | 0 | -761
1.5 | -1 | IDLE | 0 | WHEEL | BL | 0.00 | 0.00 | 0 | -358
1.5160000000032596 | -1 | IDLE | 0 | WHEEL | BR | 0.00 | 0.00 | 0 | 543
1.5160000000032596 | -1 | IDLE | 0 | HDG |  |  |  |  |  | 6.04 | 7.68 | 1.64
1.5160000000032596 | -1 | IDLE | 0 | WHEEL | FL | 0.00 | 0.00 | 0 | 463
1.5160000000032596 | -1 | IDLE | 0 | WHEEL | FR | 0.00 | 0.00 | 0 | -761
1.5160000000032596 | -1 | IDLE | 0 | WHEEL | BL | 0.00 | 0.00 | 0 | -358
1.5160000000032596 | -1 | IDLE | 0 | WHEEL | BR | 0.00 | 0.00 | 0 | 543
1.5160000000032596 | -1 | IDLE | 0 | HDG |  |  |  |  |  | 6.04 | 7.68 | 1.64
1.5320000000065193 | -1 | IDLE | 0 | WHEEL | FL | 0.00 | 0.00 | 0 | 463
1.5320000000065193 | -1 | IDLE | 0 | WHEEL | FR | 0.00 | 0.00 | 0 | -761
1.5320000000065193 | -1 | IDLE | 0 | WHEEL | BL | 0.00 | 0.00 | 0 | -358
1.5320000000065193 | -1 | IDLE | 0 | WHEEL | BR | 0.00 | 0.00 | 0 | 543
1.5320000000065193 | -1 | IDLE | 0 | HDG |  |  |  |  |  | 6.04 | 7.68 | 1.64
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
